btodcox/OpenScoreboard/Pics/IMG_0201.JPG

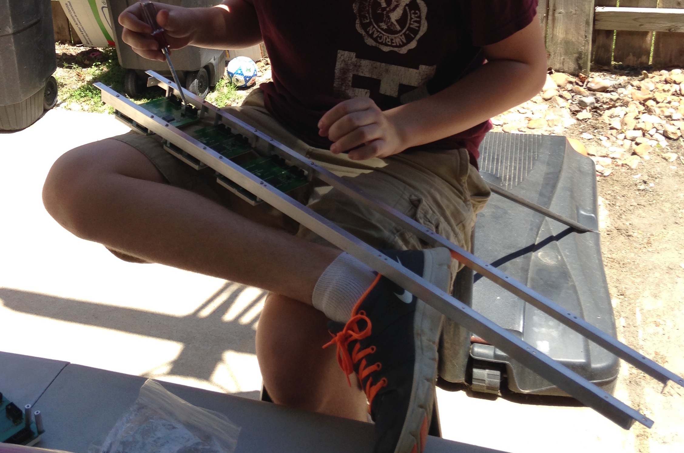
Pics/IMG_0201.JPG
