btodcox/OpenScoreboard/Pics/IMG_0209.JPG

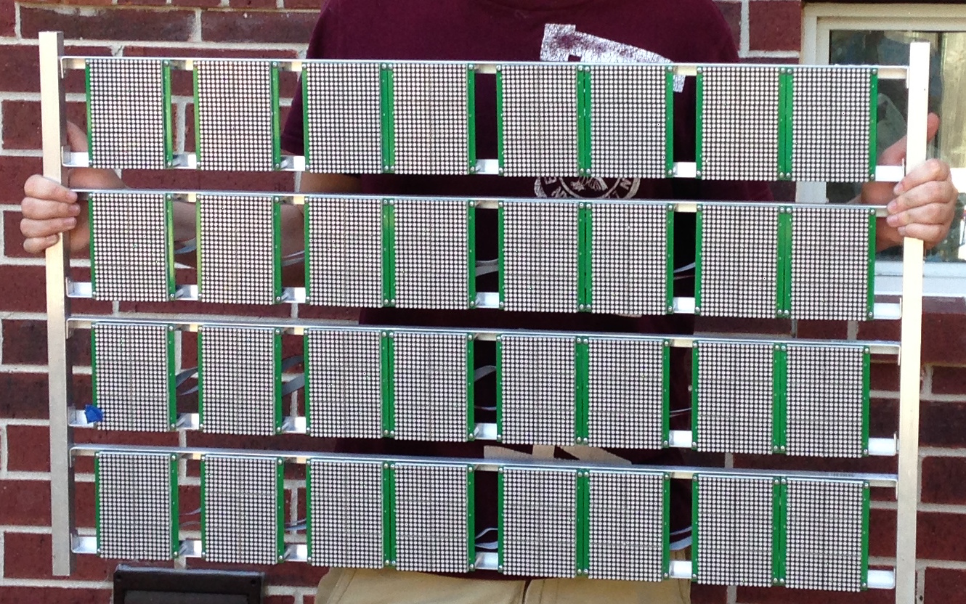
Pics/IMG_0209.JPG
