btodcox/OpenScoreboard/Pics/IMG_0256.JPG

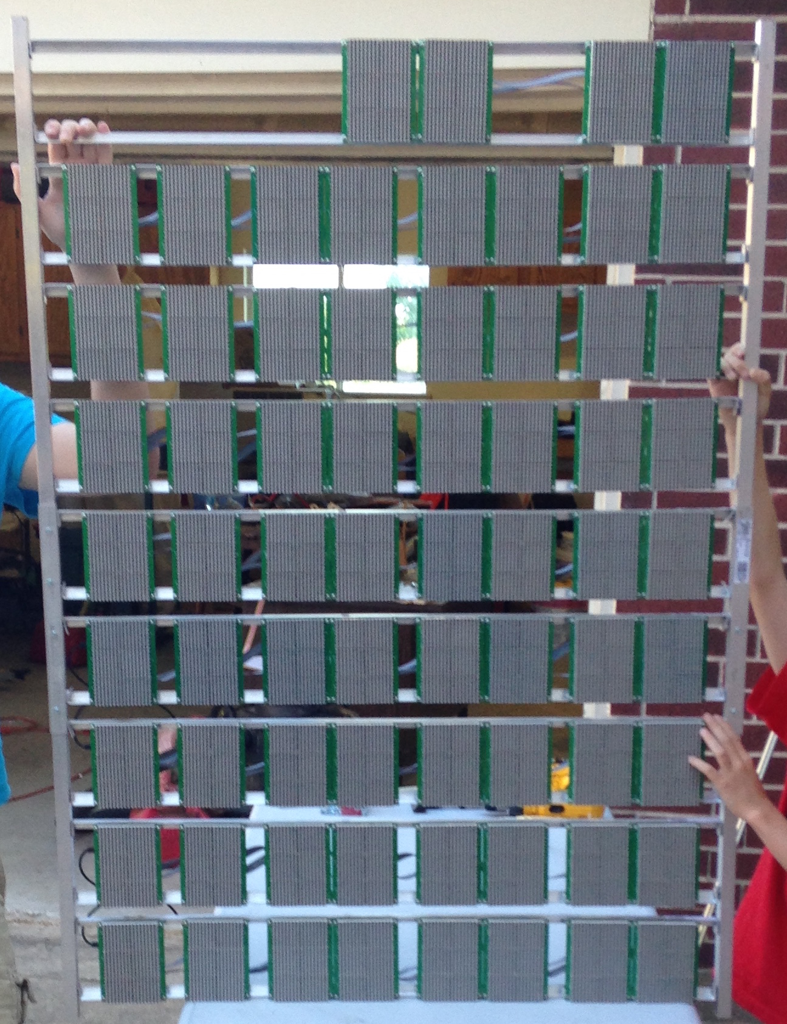
Pics/IMG_0256.JPG
