btodcox/OpenScoreboard/Pics/IMG_0265.JPG

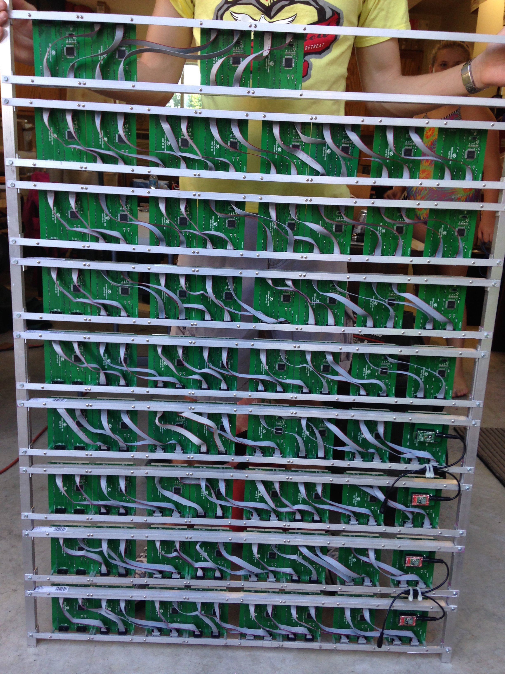
Pics/IMG_0265.JPG
