btodcox/OpenScoreboard/Pics/IMG_0523.JPG

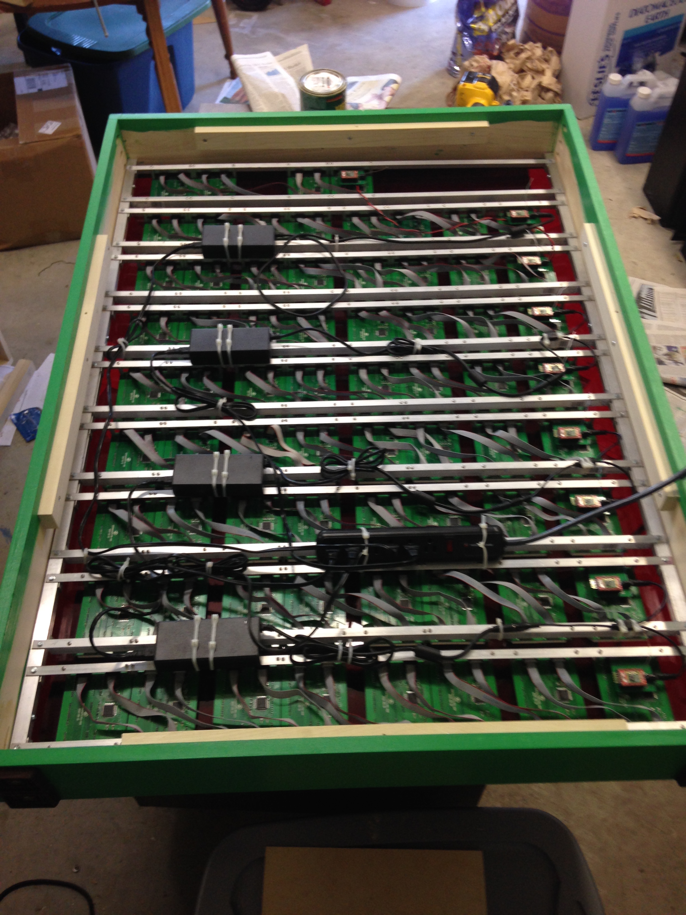
Pics/IMG_0523.JPG
