btodcox/OpenScoreboard/Software/Moteino/remote/eeprom/eeprom_write_id.ino

/*
 * EEPROM Write
 *
 * Stores values read from analog input 0 into the EEPROM.
 * These values will stay in the EEPROM when the board is
 * turned off and may be retrieved later by another sketch.
 */

#include <EEPROM.h>

// the current address in the EEPROM (i.e. which byte
// we're going to write to next)
int addr = 0;

void setup()
{
    EEPROM.write(addr, 1);
}

void loop()
{
 
}
